MakerLabsVan/ACM/Documentation/tests/wifi_test/wifi_test.ino

#include <SoftwareSerial.h>

SoftwareSerial ESP(2,3);

void setup() {
    Serial.begin(9600);
    ESP.begin(9600);
    pinMode(4, OUTPUT);
    digitalWrite(9, LOW);
    delay(500);
    digitalWrite(9, HIGH);
}

void loop() {

    while (ESP.available()) {
        Serial.write(ESP.read());
    }
    // This is for manual commands
    while (Serial.available()) {
        ESP.write(Serial.read());
    }

}

void connectWiFi(void) {
    ESP.write("AT+CWQAP\r\n");
    delay(50);
    ESP.write("AT+CWMODE=1\r\n");
    delay(50);
    ESP.write("AT+CWJAP=\"MakerLabs\",\"ecordova\"\r\n");
    while(!ESP.find("WIFI GOT IP"));
    Serial.write("Connected. ");
    while(!ESP.find("OK"));
    Serial.write("Ready.\n\n");
}

void startConnection(void) {
    Serial.write("Connecting...\n");
    ESP.write("AT+CIPMUX=1\r\n");
    delay(50);
    ESP.write("AT+CIPSTART=0,\"TCP\",\"www.httpbin.org\",80\r\n");
    while(!ESP.find("CONNECT"));
    while(!ESP.find("OK"));
    Serial.write("Connection established.\n\n");
    
}

void closeConnection(void) {
    Serial.write("Closing connection...\n");
    ESP.write("AT+CIPCLOSE=0\r\n");
    while(!ESP.find("CLOSED"));
    while(!ESP.find("OK"));
    Serial.write("Connection closed.\n\n");
}

void GET(void) {
    ESP.write("AT+CIPSEND=0,43\r\n");
    while(!ESP.find("ERROR"));
    ESP.write("AT+CIPSEND=0,43\r\n");
    delay(50);
    ESP.write("GET /ip HTTP/1.1\r\nHost: www.httpbin.org\r\n\r\n");
}

void POST(void) {
    ESP.write("AT+CIPSEND=0, 128");
    while(!ESP.find("ERROR"));
    ESP.write("AT+CIPSEND=0, 128");
    delay(50);
    ESP.write("POST /post HTTP/1.1\r\nHost: www.httpbin.org\r\nContent-Type: application/x-www-form-urlencoded\r\nContent-Length: 10\r\n\r\namount=120\r\n\r\n");
}
